SolderedElectronics/Dasduino-CONNECT-hardware-design/OUTPUTS/V1.1.1/333034.jpg

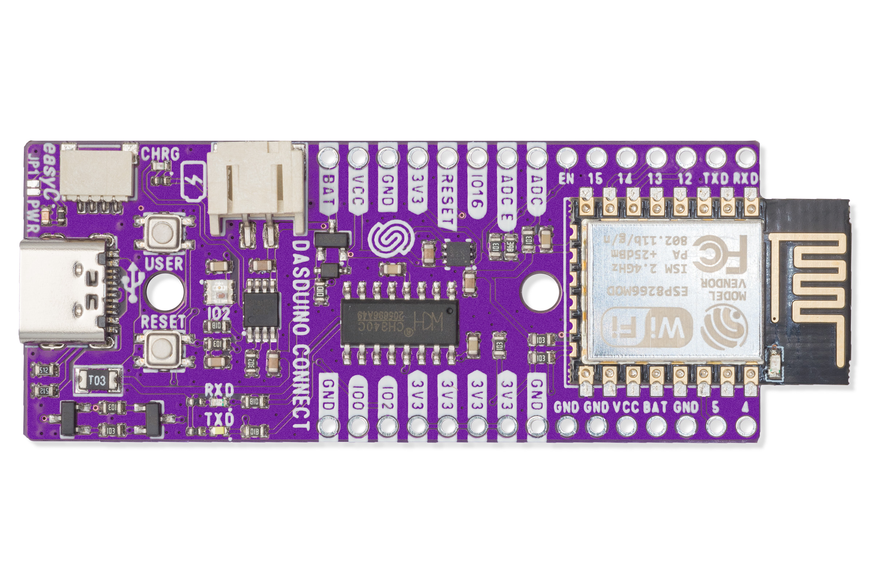
OUTPUTS/V1.1.1/333034.jpg
