SolderedElectronics/Dasduino-CONNECT-hardware-design/OUTPUTS/V1.1.1/333034 (2).jpg

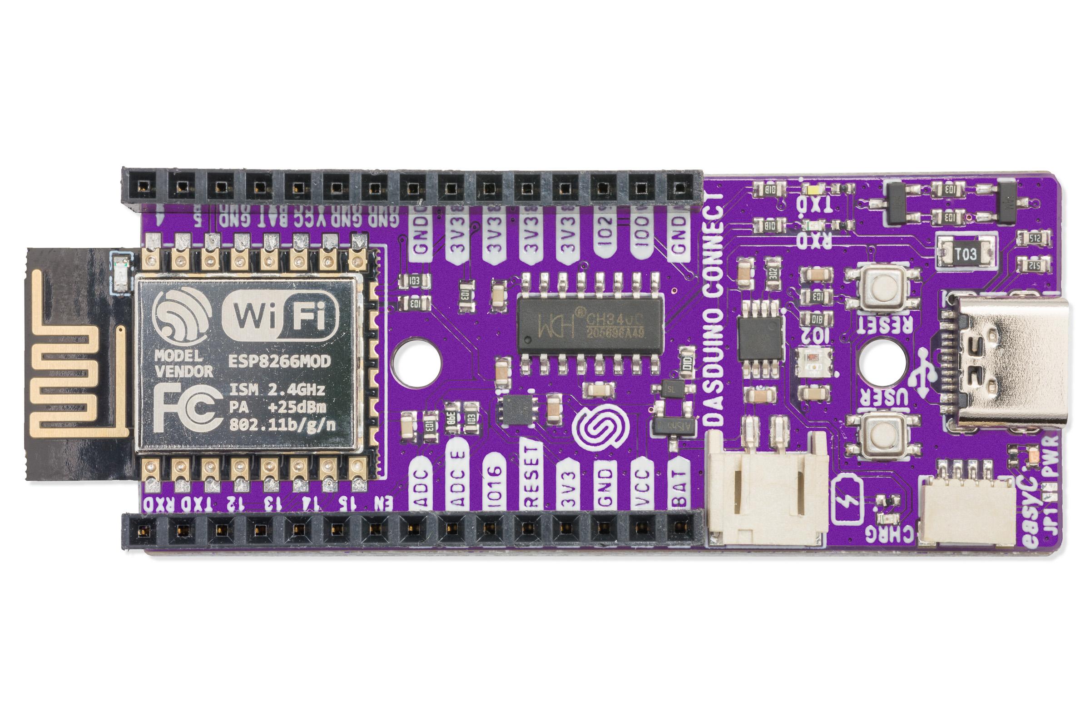
OUTPUTS/V1.1.1/333034 (2).jpg
