SolderedElectronics/Dasduino-CONNECT-hardware-design/OUTPUTS/V1.1.1/Dasduino CONNECT Pinout.jpg

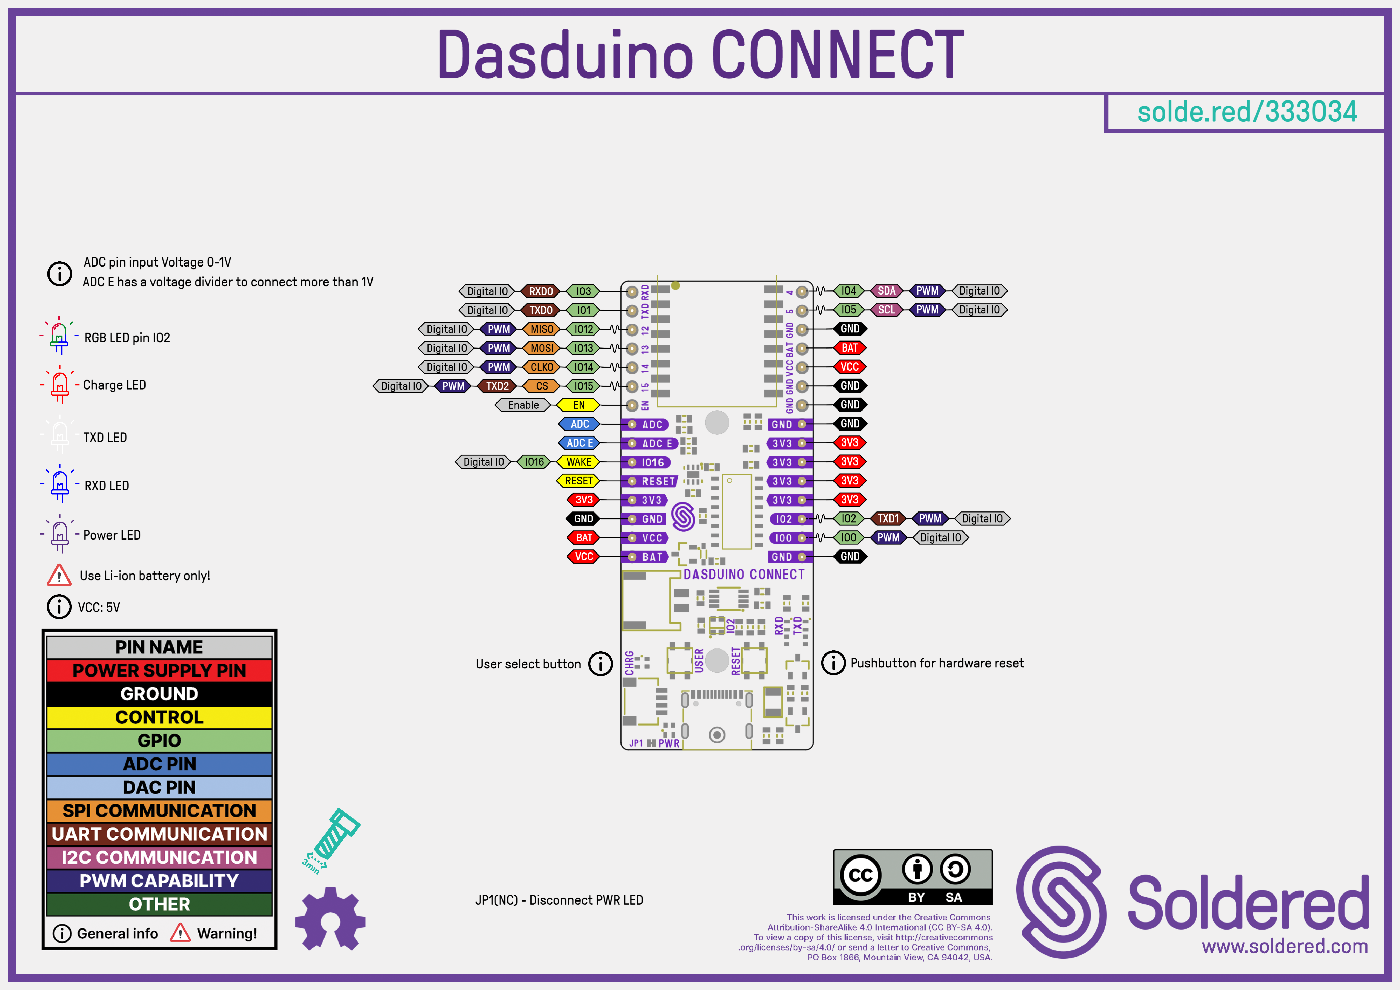
OUTPUTS/V1.1.1/Dasduino CONNECT Pinout.jpg
